tekyinblack/L0Cost-Robot/LocalController/Pico/Pictures/readme

Picture of the Pico version of the local controller design will be held here
