tekyinblack/L0Cost-Robot/LocalController/Pico/Code/readme

Code for the Pico version of the local controller will appear here
