tekyinblack/L0Cost-Robot/LocalController/Arduino/Pictures/Readme

This folder contains pictures of a version of the Local Controller board
