tekyinblack/L0Cost-Robot/LocalController/Arduino/Code/Readme

Code for the Local Controller to be compiled using the Arduino IDE
