tekyinblack/L0Cost-Robot/RobotVersions/Sokoban/3Dprinterfiles/Readme

The physical design for this robot was made on the Tinkercad platform here https://www.tinkercad.com/things/iRz2ZUdj2B9-sokoban-robot
These are the stl files created fron this design for convenience but anyone is free to copy teh design and amend as required.
