tekyinblack/L0Cost-Robot/RobotVersions/Sokoban/3Dprinterfiles/Sokoban Robot Horizontal Camera Mount.stl

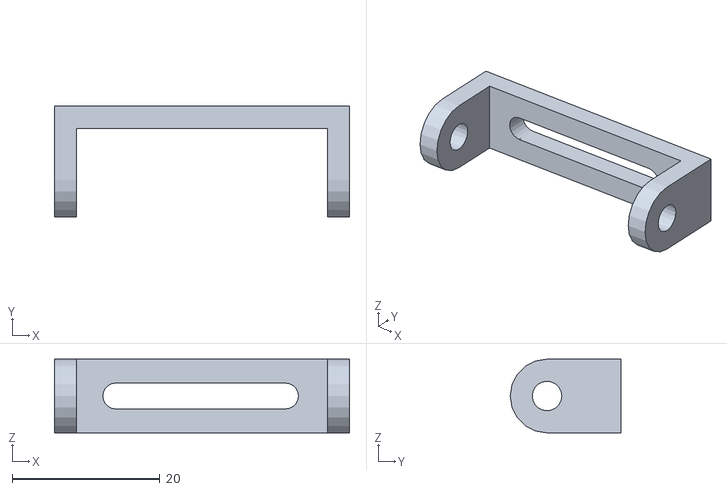
[picture p19: CAD file, 2023-11-26]
RobotVersions/Sokoban/3Dprinterfiles/Sokoban Robot Horizontal Camera Mount.stl
40.0 x 15.0 x 10.0
